VersBinarii/radiant/src/lib.rs

#![no_main]
#![no_std]

use defmt_rtt as _; // global logger

// TODO(5) adjust HAL import
// use some_hal as _; // memory layout

use panic_probe as _;

pub mod dummy_pin;
pub mod gui;
pub mod peripherals;

// same panicking *behavior* as `panic-probe` but doesn't print a panic message
// this prevents the panic message being printed *twice* when `defmt::panic` is invoked
#[defmt::panic_handler]
fn panic() -> ! {
    cortex_m::asm::udf()
}

/// Terminates the application and makes `probe-run` exit with exit-code = 0
pub fn exit() -> ! {
    loop {
        cortex_m::asm::bkpt();
    }
}

// defmt-test 0.3.0 has the limitation that this `#[tests]` attribute can only be used
// once within a crate. the module can be in any file but there can only be at most
// one `#[tests]` module in this library crate
#[cfg(test)]
#[defmt_test::tests]
mod unit_tests {
    use defmt::assert;

    #[test]
    fn it_works() {
        assert!(true)
    }
}
